go4retro/Nu2031/ref/vc1541-ieee/vc1541-ieee.png

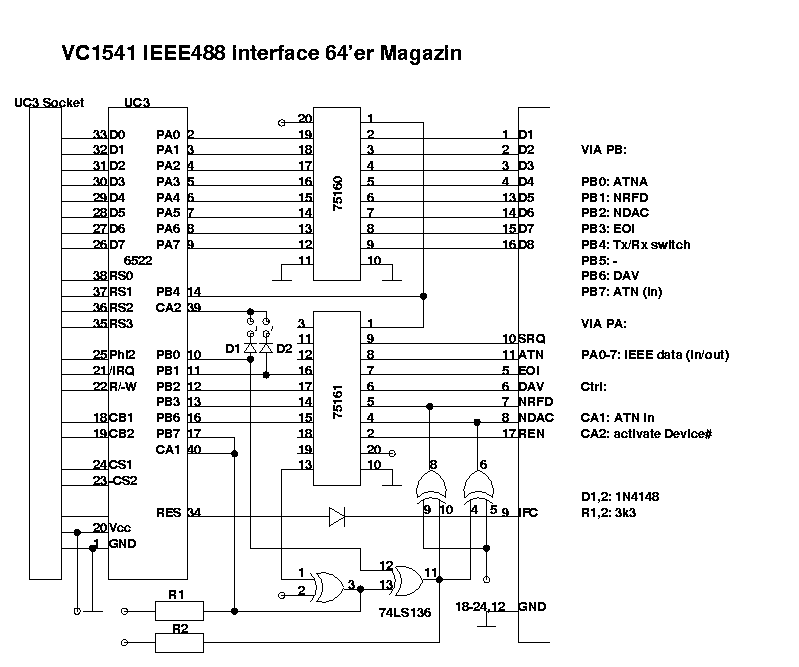
ref/vc1541-ieee/vc1541-ieee.png
